SeanPeterson/SeanBoy/Img/IMG_20151020_160948.jpg

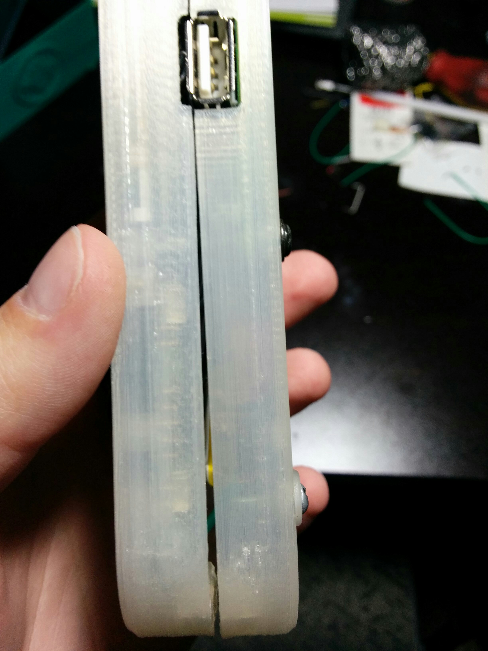
Img/IMG_20151020_160948.jpg
