SeanPeterson/SeanBoy/Img/IMG_20151020_161237.jpg

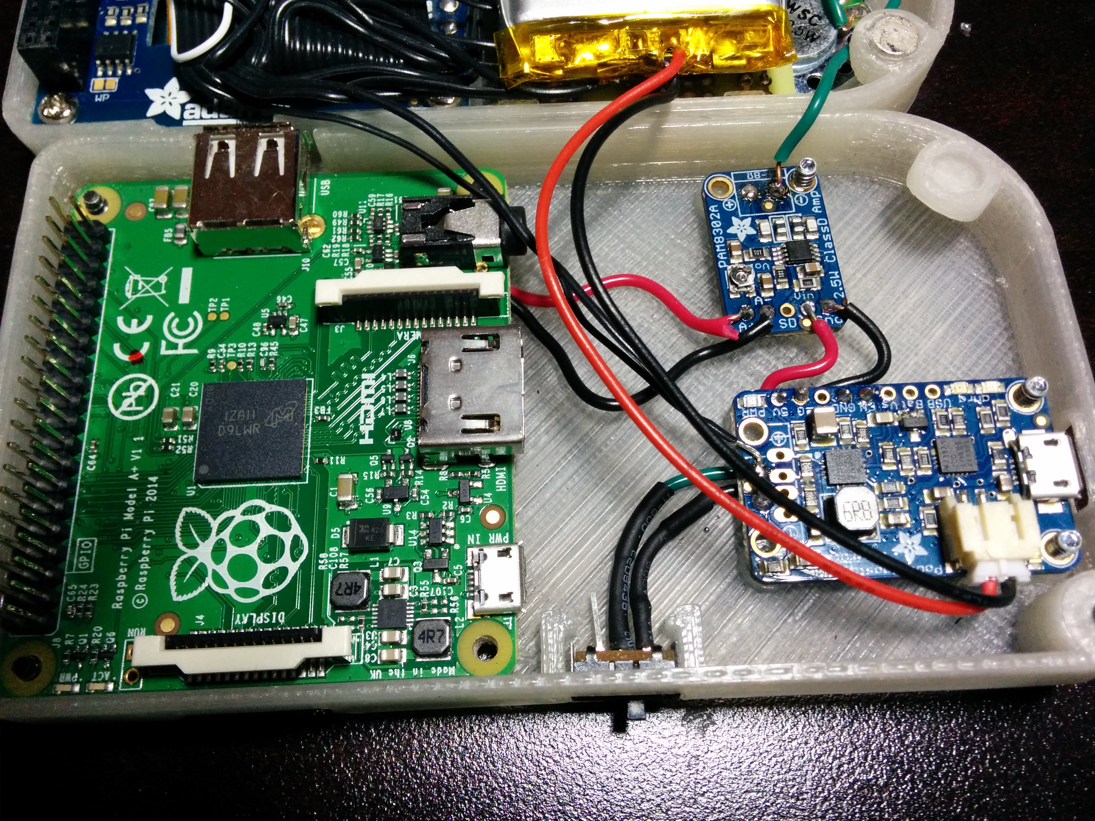
Img/IMG_20151020_161237.jpg
