SeanPeterson/SeanBoy/Img/IMG_20151020_161250.jpg

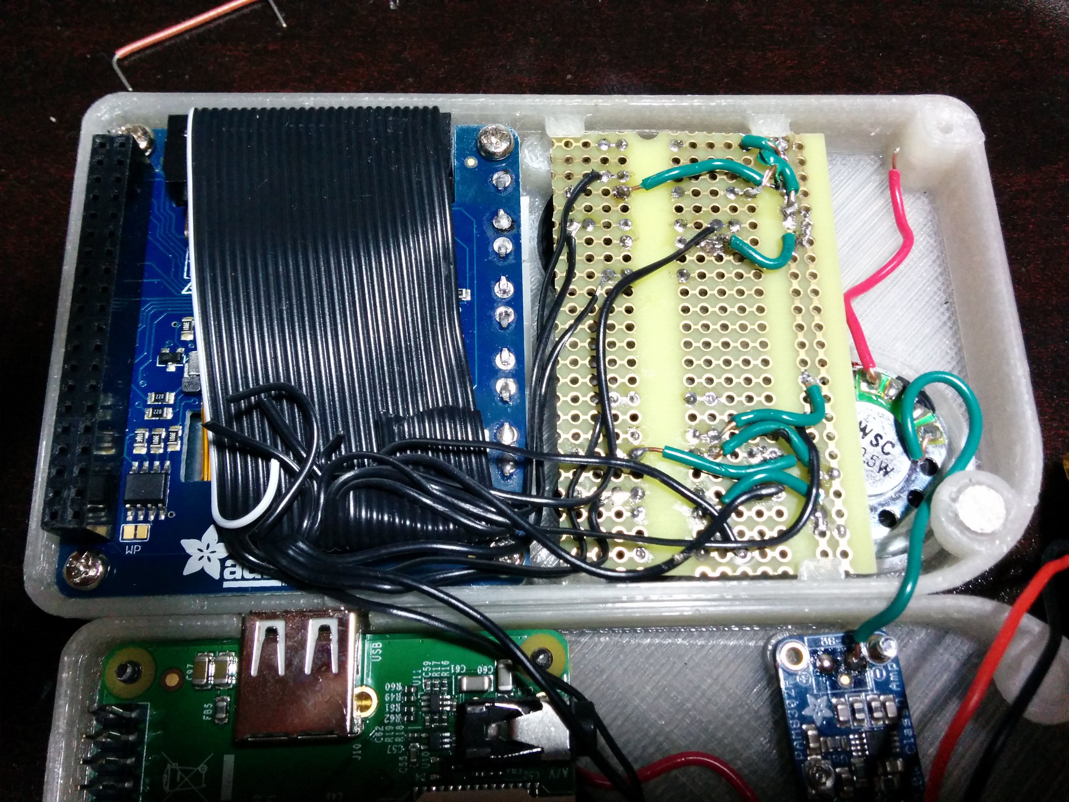
Img/IMG_20151020_161250.jpg
